MG-5/alarm-clock_hardware/LTspice/high-side-switch.asc

Q1: npn
Q2: pnp
R1: res; 220k
R2: res; 100k
R3: res; 10k
R4: res; 1k
V1: voltage; PULSE(0 3.3 1m 10u 10u 1m 2m)
V2: voltage; 24V
Named nets: 0
.tran 10m startup
