MG-5/alarm-clock_hardware/LTspice/LT3757_Boost-35V.asc

C1: cap; 470n
C2: cap; 1n
C3: polcap; 10µ
C4: cap; 47n
C5: cap; 22p
C6: cap; 10n
D1: diode; ES1D
I1: load2; PULSE(0 20m 3m 20µ 20µ 1000µ 1.05m)
L1: ind; 470µ; Rser=170m
Q1: NMOS; FDS2734
R1: RES; 24.3k
R2: res; 13k
R3: res; 270k
R4: res; 56k
R5: res; 43.2K
R6: res; 200K
R7: res; 10m
R8: res; 22
Rload: res; 1000000k
U1: LT3757
V1: VOLTAGE; PWL(0 24 10ms 24 11ms 9); Rser=1
Named nets: 0, OUT, IN
.tran 20m startup
LT3757 - Boost, Flyback, SEPIC and Inverting Controller
Input: 8-24V       Output: 35V@25mA
